Raf1nhaM5869/Mini-ind-stria/src/asseats/IMG.jpeg

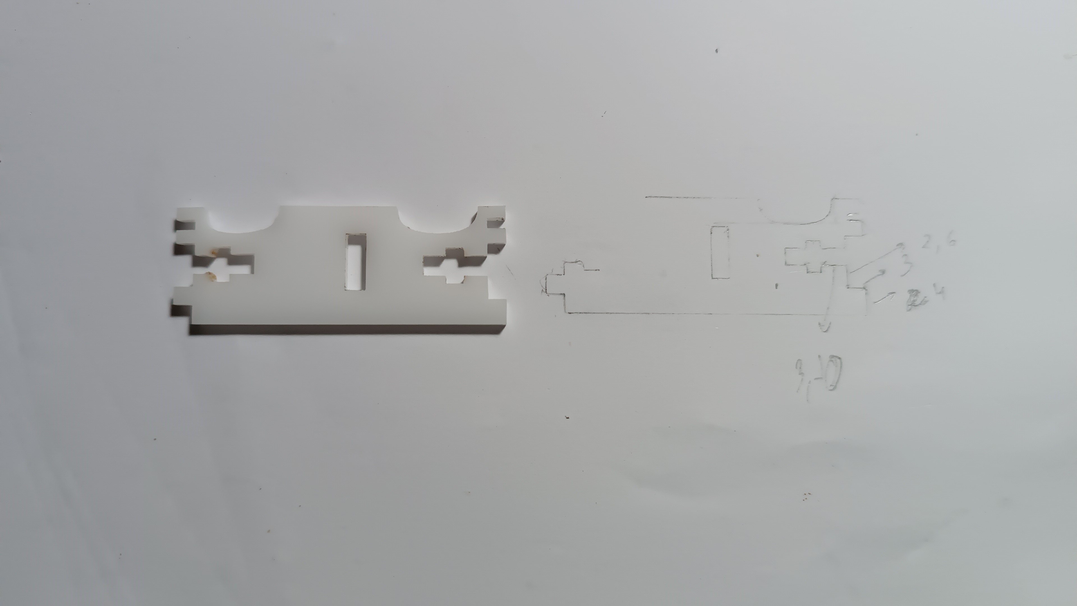
src/asseats/IMG.jpeg
