Raf1nhaM5869/Mini-ind-stria/src/asseats/IMG_20231218_215922.jpg

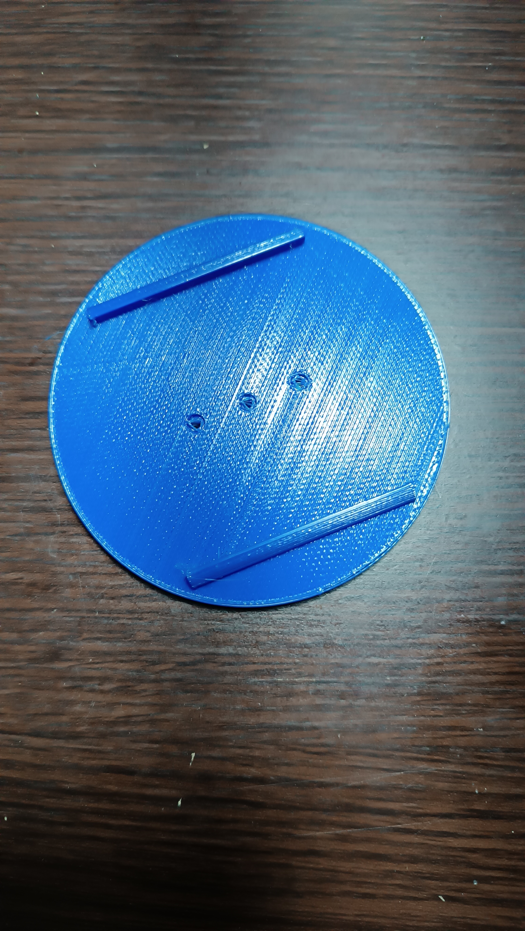
src/asseats/IMG_20231218_215922.jpg
