Raf1nhaM5869/Mini-ind-stria/src/asseats/IMG_20240115_205544.jpg

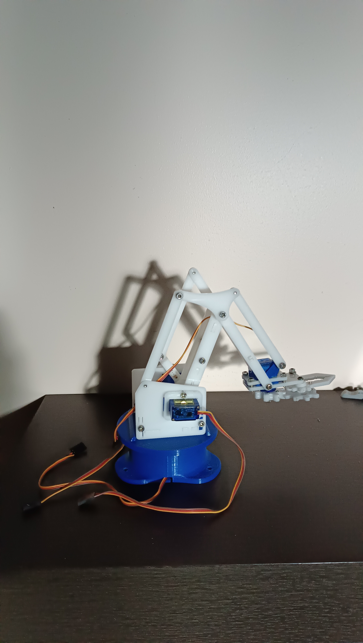
src/asseats/IMG_20240115_205544.jpg
