Raf1nhaM5869/Mini-ind-stria/src/asseats/IMG_20240409_080526.jpg

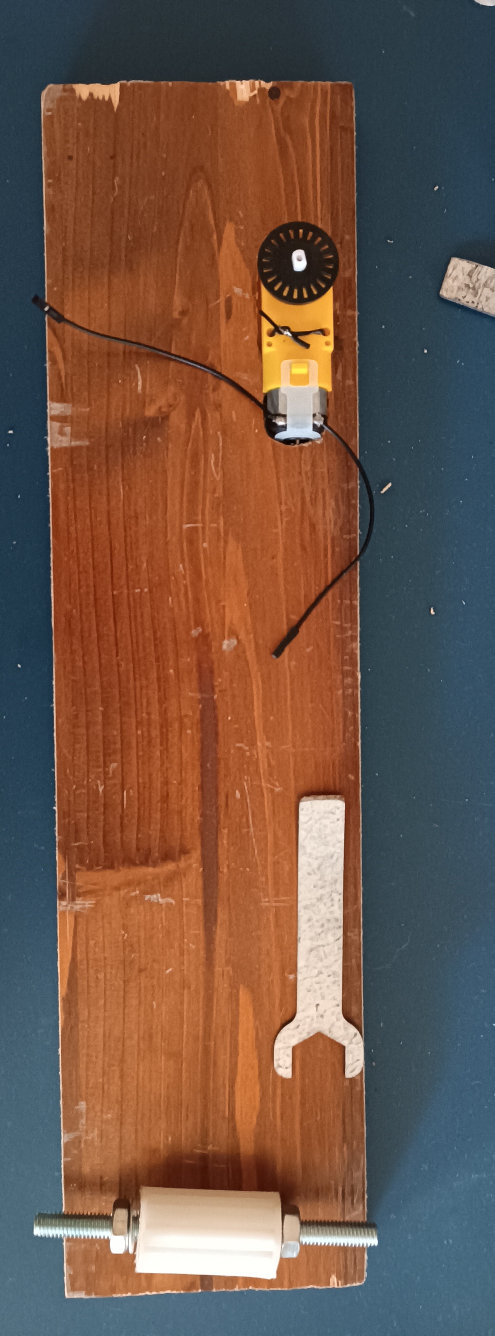
src/asseats/IMG_20240409_080526.jpg
