Raf1nhaM5869/Mini-ind-stria/src/asseats/IMG_20240428_230100.jpg

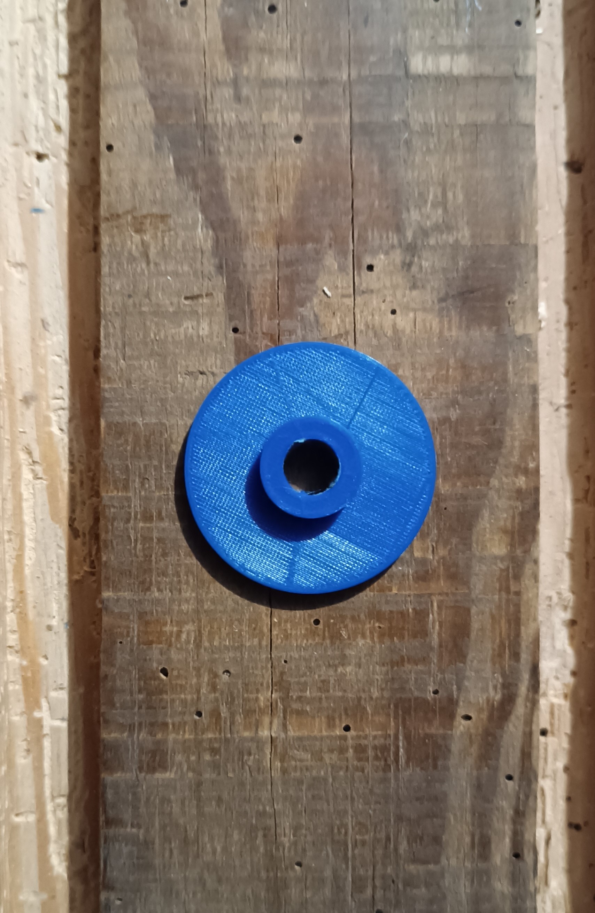
src/asseats/IMG_20240428_230100.jpg
